dakk/seatalk-wifi-remote/seatalk-wifi-remote/conf_example.h

#ifndef CONF_H
#define CONF_H

#define WIFI_SSID "MyBoatWiFi"
#define WIFI_PASSWORD "my_secret_password"

#define SEATALK_GATEWAY_IP "192.168.1.100"
#define SEATALK_GATEWAY_PORT 4001

// Debug mode: set to disable wifi
// #define DEBUG_MODE

// Inactivity timeout before auto-sleep (minutes)
#define INACTIVITY_TIMEOUT_MIN 20

#endif
